BogdanTheGeek/ESP_RC/src/Receiver/pins.h

//Contains the pinout

#if defined(SMOL_BOY_V1)

	#define V_BAT	A0

	#define CH0		0
	#define CH1 	2	
	#define CH2 	15
	#define CH3 	13
	#define CH4 	12
	#define CH5 	14

	#define DATA	4
	#define CLOCK	5

#endif
